Picatout/stm8-gamepad/KiCAD/stm8-gamepad/stm8-gamepad.kicad_sch

## KiCad design KiCAD/stm8-gamepad/stm8-gamepad.kicad_sch (2024-02-16, an earlier design)

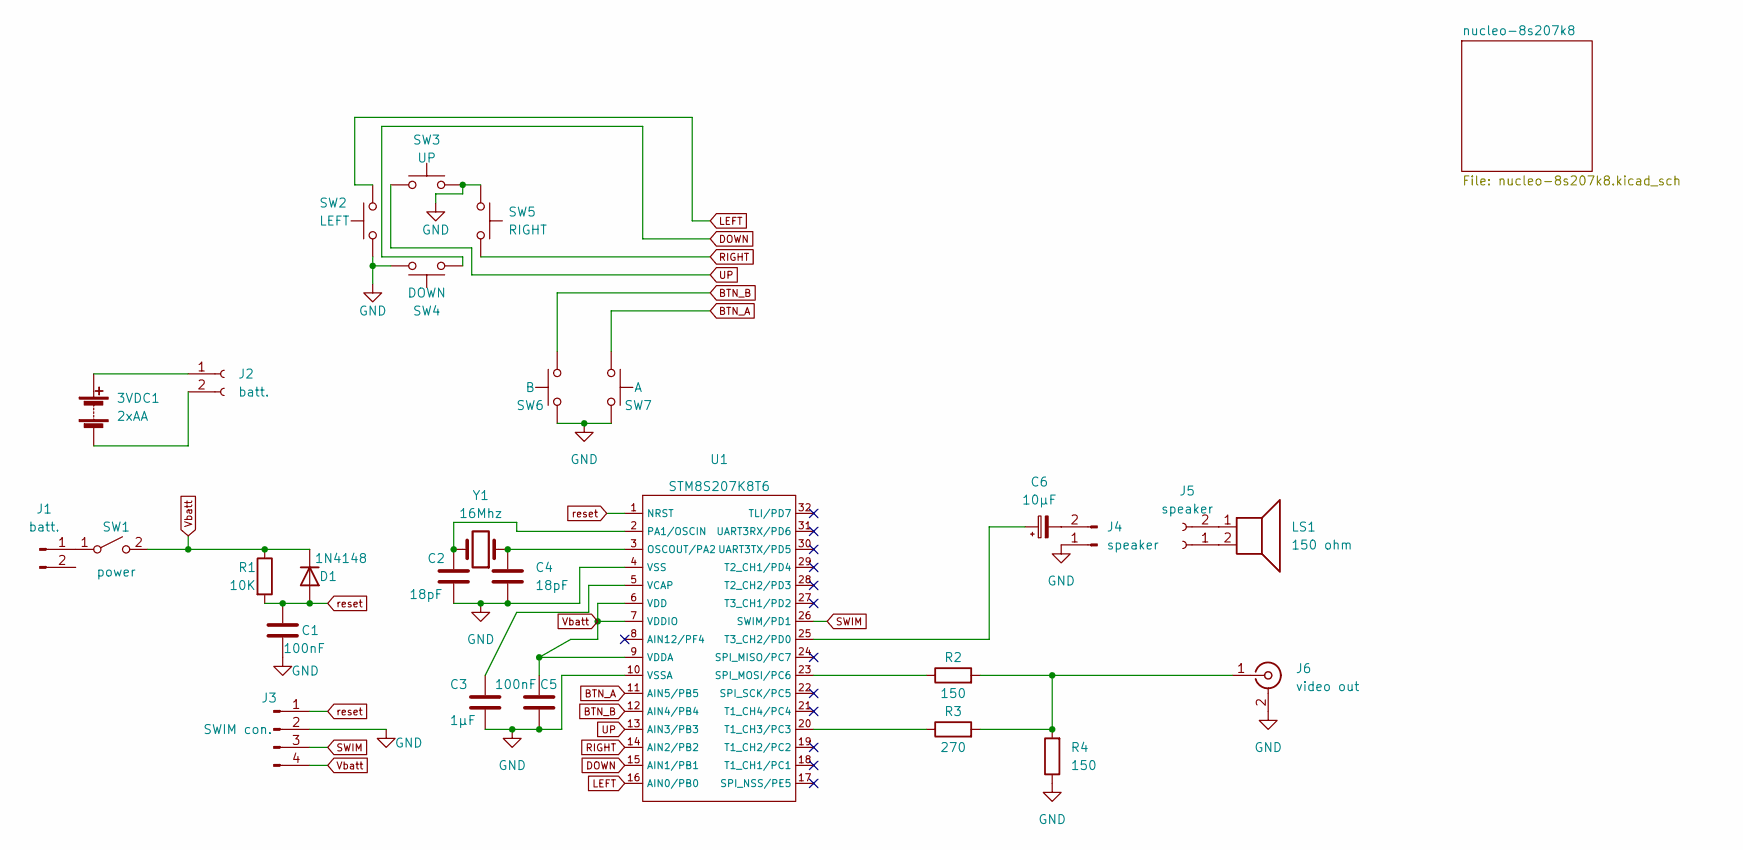
[picture p10: schematic stm8-gamepad.kicad_sch]

Parts:
3VDC1: 2xAA
C1, C5: 100nF
C2, C4: 18pF
C3: 1µF
C6: 10µF
D1: 1N4148; D_DO-35_SOD27_P7.62mm_Horizontal
J1, J2: batt.
J3: SWIM con.
J4, J5: speaker
J6: video out
LS1: 150 ohm
R1: 10K
R2, R4: 150
R3: 270
SW1: power
SW2: LEFT
SW3: UP
SW4: DOWN
SW5: RIGHT
SW6: B
SW7: A
U1: STM8S207K8T6
Y1: 16Mhz

Connections:
BTN_A: SW7.1 (A), SW7.2 (A), U1.11 (AIN5/PB5)
BTN_B: SW6.3 (B), SW6.4 (B), U1.12 (AIN4/PB4)
DOWN: SW4.1 (A), SW4.2 (A), U1.15 (AIN1/PB1)
GND: C1.2, C2.2, C3.2, C4.2, C5.2, J3.2, J4.1, J6.2 (Ext), R4.1, SW2.1 (A), SW2.2 (A), SW3.3 (B), SW3.4 (B), SW4.3 (B), SW4.4 (B), SW5.1 (A), SW5.2 (A), SW6.1 (A), SW6.2 (A), SW7.3 (B), SW7.4 (B), U1.4 (VSS), U1.10 (VSSA)
LEFT: SW2.3 (B), SW2.4 (B), U1.16 (AIN0/PB0)
unnamed: 3VDC1.1 (+), J2.1
unnamed: 3VDC1.2 (-), J2.2
unnamed: C2.1, U1.2 (PA1/OSCIN), Y1.2
unnamed: C3.1, U1.5 (VCAP)
unnamed: C4.1, U1.3 (OSCOUT/PA2), Y1.1
unnamed: C6.1, U1.25 (T3_CH2/PD0)
unnamed: C6.2, J4.2
unnamed: J1.1, SW1.1 (A)
unnamed: J5.1, LS1.2
unnamed: J5.2, LS1.1
unnamed: J6.1 (In), R2.2, R3.2, R4.2
unnamed: R2.1, U1.23 (SPI_MOSI/PC6)
unnamed: R3.1, U1.20 (T1_CH3/PC3)
RIGHT: SW5.3 (B), SW5.4 (B), U1.14 (AIN2/PB2)
SWIM: J3.3, U1.26 (SWIM/PD1)
UP: SW3.1 (A), SW3.2 (A), U1.13 (AIN3/PB3)
Vbatt: C5.1, D1.1 (K), J3.4, R1.1, SW1.2 (B), U1.6 (VDD), U1.7 (VDDIO), U1.9 (VDDA)
reset: C1.1, D1.2 (A), J3.1, R1.2, U1.1 (NRST)
