Picatout/stm8-gamepad/splash.asm

;----------------------
;  splash screen
;----------------------
BYTES_PER_IMG_ROW=25
IMG_DATA_SIZE=4800
	.area CODE

img_data:
	.byte 0xBF, 0xF5, 0x57, 0x50, 0x00, 0x05, 0x80, 0x00, 0x00, 0x00, 0x00, 0x00, 0x00, 0x00, 0x03, 0x00, 0x00, 0x00, 0x04, 0xD5, 0xEB, 0xFD, 0xFF, 0xDD, 0xFF
	.byte 0xD5, 0x5F, 0xF9, 0x00, 0x00, 0x08, 0x20, 0x00, 0x00, 0x00, 0x00, 0x00, 0x00, 0x00, 0x02, 0x00, 0x00, 0x00, 0x02, 0xBE, 0xAA, 0xFF, 0xFF, 0xFF, 0xEB
	.byte 0x7F, 0xF5, 0x6E, 0xA0, 0x00, 0x02, 0x80, 0x00, 0x00, 0x00, 0x00, 0x00, 0x00, 0x00, 0x01, 0x00, 0x00, 0x00, 0x00, 0x4B, 0xD7, 0xB7, 0xB5, 0x77, 0x7F
	.byte 0xD5, 0x5F, 0xDA, 0x00, 0x00, 0x00, 0x00, 0x00, 0x00, 0x00, 0x00, 0x00, 0x00, 0x00, 0x02, 0x00, 0x00, 0x00, 0x00, 0x35, 0x6B, 0xFE, 0xFF, 0xFD, 0xDF
	.byte 0xBF, 0xFB, 0x76, 0x80, 0x00, 0x00, 0x00, 0x00, 0x00, 0x00, 0x00, 0x00, 0x00, 0x00, 0x00, 0x00, 0x00, 0x00, 0x00, 0x0F, 0xD5, 0xFF, 0xFF, 0xDF, 0xFB
	.byte 0xD5, 0x5E, 0xDA, 0x00, 0x00, 0x00, 0x00, 0x00, 0x00, 0x00, 0x00, 0x00, 0x00, 0x00, 0x00, 0x00, 0x00, 0x00, 0x00, 0x2A, 0xD7, 0x5B, 0xDB, 0x77, 0xBF
	.byte 0x7F, 0xFB, 0x6A, 0x80, 0x00, 0x00, 0x00, 0x00, 0x00, 0x00, 0x00, 0x00, 0x00, 0x00, 0x00, 0x00, 0x00, 0x00, 0x00, 0x07, 0xA1, 0xFF, 0x7F, 0xFE, 0xFF
	.byte 0xD5, 0x57, 0xD2, 0x00, 0x00, 0x00, 0x00, 0x00, 0x00, 0x00, 0x00, 0x00, 0x00, 0x00, 0x00, 0x00, 0x00, 0x00, 0x00, 0x15, 0x56, 0xFF, 0xFD, 0xDF, 0xEB
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
	.byte 0x00, 0x00, 0x00, 0x00, 0x00, 0x00, 0x00, 0x02, 0x08, 0x91, 0x21, 0x00, 0x00, 0x00, 0x12, 0x48, 0x00, 0x90, 0x00, 0x00, 0x20, 0x08, 0x48, 0x00, 0x00
	.byte 0x00, 0x00, 0x00, 0x00, 0x00, 0x00, 0x00, 0x20, 0x82, 0x00, 0x04, 0x24, 0xA9, 0x49, 0x00, 0x00, 0x00, 0x02, 0x49, 0x10, 0x00, 0x01, 0x00, 0x00, 0x00
	.byte 0x00, 0x00, 0x00, 0x00, 0x00, 0x00, 0x00, 0x02, 0x48, 0x00, 0x00, 0x00, 0x00, 0x00, 0x00, 0x00, 0x00, 0x00, 0x00, 0x00, 0x00, 0x00, 0x00, 0x00, 0x00
	.byte 0x00, 0x00, 0x00, 0x00, 0x00, 0x00, 0x00, 0x00, 0x00, 0x00, 0x00, 0x00, 0x00, 0x00, 0x00, 0x00, 0x00, 0x00, 0x00, 0x00, 0x00, 0x00, 0x00, 0x00, 0x00
