Picatout/stm8-gamepad/app.asm

;---------------------------------------
; move memory block 
; input:
;   X 		destination 
;   Y 	    source 
;   acc16	bytes count 
; output:
;   X       destination 
;--------------------------------------
	INCR=1 ; incrament high byte 
	LB=2 ; increment low byte 
	VSIZE=2
move::
	push a 
	pushw x 
	_vars VSIZE 
	clr (INCR,sp)
	clr (LB,sp)
	pushw y 
	cpw x,(1,sp) ; compare DEST to SRC 
	popw y 
	jreq move_exit ; x==y 
	jrmi move_down
move_up: ; start from top address with incr=-1
	addw x,acc16
	addw y,acc16
	cpl (INCR,sp)
	cpl (LB,sp)   ; increment = -1 
	jra move_loop  
move_down: ; start from bottom address with incr=1 
    decw x 
	decw y
	inc (LB,sp) ; incr=1 
move_loop:	
	addw x,(INCR,sp)
	addw y,(INCR,sp) 
	ld a,(y)
	ld (x),a 
	pushw x 
	_ldxz acc16 
	decw x 
	_strxz acc16 
	popw x 
	jreq move_exit  
	jra move_loop
move_exit:
	_drop VSIZE
	popw x 
	pop a 
	ret 	

;--------------------
; fill memory block 
; input: 
;     A   fill value 
;     X   count 
;     Y   addr (incr)
;---------------------
fill:
	tnzw x 
	jreq 9$
1$:	ld (y),a 
	incw y 
	decw x 
	jrne 1$
9$:	ret 

;----------------------
; .asciz string length 
; input:
;    Y    *string 
; output:
;    A    length 
;    Y    unchanged 
;----------------------
strlen:
	pushw y 
	push #0
1$: ld a,(y)
	jreq 2$
	inc (1,sp)
	incw y 
	jra 1$ 
2$:  
	pop a 
	popw y 
	ret 

;------------------------
; load bitmap data in 
; tv_buffer 
; image is upside down 
; input:
;    A   byte per ROW
;    X   data size 
;    Y   data address 
;------------------------
	YCOOR=1 ; video graphic row 
	COUNT=YCOOR+2 ; data size 
	ROW_CNTR=COUNT+2 ; bytes per row 
	VAR_SIZE=ROW_CNTR+1
load_bmp:
	_vars VAR_SIZE
	clr (ROW_CNTR,sp)
	ld (ROW_CNTR+1,sp),a  
	ldw (COUNT,sp),x
	ldw x,#VRES 
	ldw (YCOOR,sp),x 
1$: ; copy ROW_CNTR bytes 
	dec (YCOOR+1,sp)
	jreq 9$
	ldw x,(YCOOR,sp) 
	ld a,(ROW_CNTR+1,sp)
	_straz acc8 
	mul x,a 
	addw x,#tv_buffer
2$: ld a,(y)
	ld (x),a 
	incw x 
	incw y 
	_decz acc8 
	jrne 2$
	ldw x,(COUNT,sp)
	subw x,(ROW_CNTR,sp)
	ldw (COUNT,sp),x
	jrugt 1$ 
9$:	_drop VAR_SIZE
	ret 

;------------------------
; print version string 
;-----------------------
put_version:
	ld a,#'V 
	call tv_putc
	ldw x,#MAJOR 
	call put_uint16
	ld a,#'. 
	call tv_putc 
	ldw x,#MINOR
	call put_uint16
	ld a,#'R 
	call tv_putc 
	ldw x,#REV 
	call put_uint16
	ret 

version_str: .asciz "STM8 game console, "
cright: .asciz "(C) Jacques Deschenes, 2023,24"

;------------------------
; display prompt asking 
; player for another 
; round or quit.
;  input: text position  
;    XL   xcoord 
;    XH   ycoord 
;------------------------
ask_str:
.asciz "A) Play again\rB) main menu"

again:
	pushw x 
	_strxz cy
	ld a,xh  
	call clr_text_line
	ld a,(1,sp) 
	inc a 
	call clr_text_line  
	ldw y,#ask_str 
	call tv_puts 
	_drop 2 
1$: ldw x,#255 
	call wait_key_release
	call wait_key  
	cp a,#BTN_A 
	jreq 9$
	cp a,#BTN_B 
	jrne 1$ 
9$: 
	ldw x,#255 
	call wait_key_release 
	ret 


SCROLL_DLY=2
;--------------------------
; application entry point 
;--------------------------
main:
.if DEBUG  
	call uart_cls 
	ldw x,#version_str 
	call uart_puts
	ld a,#CR 
	call uart_putc
.endif ;; DEBUG 
	call beep
	call tv_cls
; show splash screen 
	ld a,#BYTES_PER_IMG_ROW
	ldw x,#IMG_DATA_SIZE
	ldw y,#img_data
	call load_bmp
	ld a,#60 
	call pause 
	call scroll_text_up 
	ld a,#LINE_PER_SCREEN-1 
	_straz cy 
	_clrz cx 
	ldw y,#version_str 
	call tv_puts
	call put_version
	ld a,#8*SCROLL_DLY 
	call pause 
	call scroll_text_up   
	ld a,#8*SCROLL_DLY
	call pause  
	ld a,#LINE_PER_SCREEN-1
	_straz cy 
	_clrz cx 
	ldw y,#cright 
	call tv_puts
    ld a,#SCROLL_DLY
	call roll_up 
2$:	ldw y,#prog_list
    call menu 
    call (x)
    jra 2$ 

;---------------------------
; display list of games
; input:
;    Y   menu items 
;--------------------------
	GAM_ADR=1
	KPAD=GAM_ADR+16
	SEL=KPAD+1 
	COUNT=SEL+1
	VAR_SIZE=COUNT 	
menu:
	_vars VAR_SIZE 
	clr (SEL,sp)
	clr (COUNT,sp)
	ldw x,sp 
	incw x 
	_strxz ptr16 
	call tv_cls  
; build games list on stack     
1$: ld a,(y)
    jreq user_select 
	ld a,(COUNT,sp)
	ld xh,a 
	ld a,#SPACE  
	call select_mark 
	call tv_puts  
	incw y 
	ld a,(COUNT,sp)
	sll a 
	clrw x 
	ld xl,a 
	ld a,(y)
	incw y 
	ld ([ptr16],X),a 
	incw x 
	ld a,(y)
	incw y 
	ld ([ptr16],x),a
	inc (COUNT,sp)
	jra 1$ 
; display selection cursor and 
; wait for user input    
user_select:
    ldw x,#0x200 
	call wait_key_release
	ld a,(SEL,sp)
	ld xh,a 
	ld a,#'>
	call select_mark
	call wait_key 
	ld (KPAD,sp),a
	ld a,(SEL,sp)
	ld xh,a
	ld a,#SPACE 
	call select_mark
	ld a,(KPAD,sp)
	and a,#BTN_DOWN ; down button? 
	jreq 4$ 
; down button 
	ld a,(SEL,sp)
	inc a 
	cp a,(COUNT,sp)
	jreq user_select
	ld (SEL,sp),a 
	jra user_select 
; up button ?
4$: 
	ld a,(KPAD,sp)
	and a,#BTN_UP
	jreq 6$ 
	ld a,(SEL,sp)
	dec a 
	jrmi user_select 
	ld (SEL,sp),a 
	jra user_select 
6$:
	ld a,(KPAD,sp)
	and a,#BTN_A
	jreq user_select
	ldw x,#255
	call wait_key_release 
	ld a,(SEL,sp)
	sll a 
	clrw x 
	ld xl,a 
	ldw x,([ptr16],x)
	_drop VAR_SIZE 
	ret 

;-------------------------------
; display or erase 
; selection marker 
; input:
;    A    char to diplay 
;    XH   selected item {0..7}
;------------------------------
select_mark:
    push a 
    clr a 
    ld xl,a 
	_strxz cy 
    pop a 
	call tv_putc 
	ret 


prog_list:
; tetris like game, but it's not. 
fall_name:
.asciz "FALL"
.word fall
; mastermind variant game 
lock_name:
.asciz "CADENA"
.word lock_game 
; a snake game variation
.asciz "SNAKE"
.word snake
; John Conway game of life simulation
.asciz "CONWAY"
.word game_of_life
.word 0 
